thingSoC/TSOC_ESP32S/TSOC_ESP32S/eagleUp/eagleUp_TSOC_ESP32S_board_top.jpg

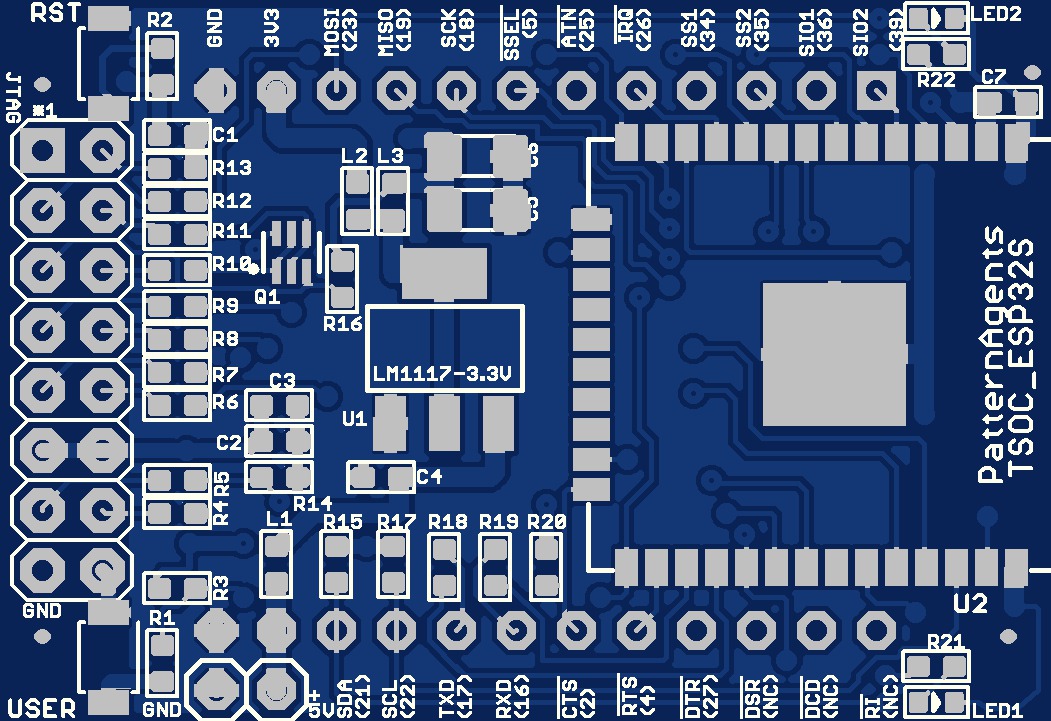
TSOC_ESP32S/eagleUp/eagleUp_TSOC_ESP32S_board_top.jpg
