thingSoC/TSOC_ESP32S/TSOC_ESP32S/images/product/Blynk_Screen_ESP32.jpg

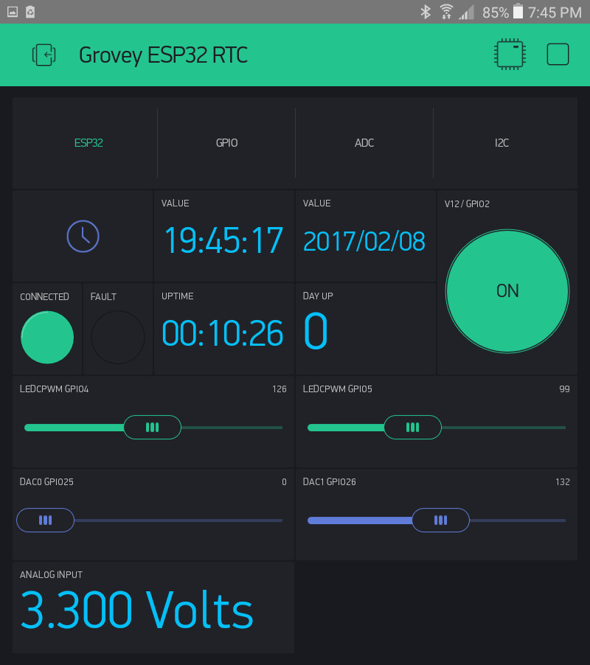
TSOC_ESP32S/images/product/Blynk_Screen_ESP32.jpg
