thingSoC/TSOC_ESP32S/TSOC_ESP32S/images/product/Screenshot_ESP32.jpg

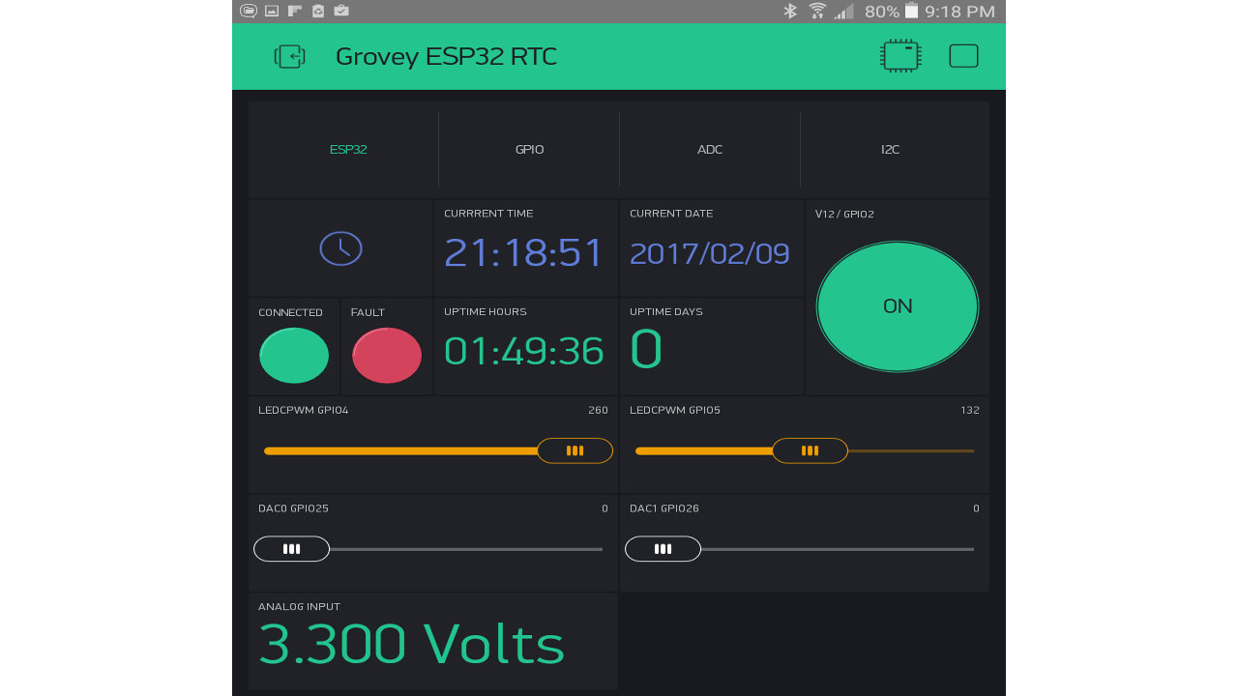
TSOC_ESP32S/images/product/Screenshot_ESP32.jpg
