thingSoC/TSOC_ESP32S/TSOC_ESP32S/images/product/Screenshot_GPIO.jpg

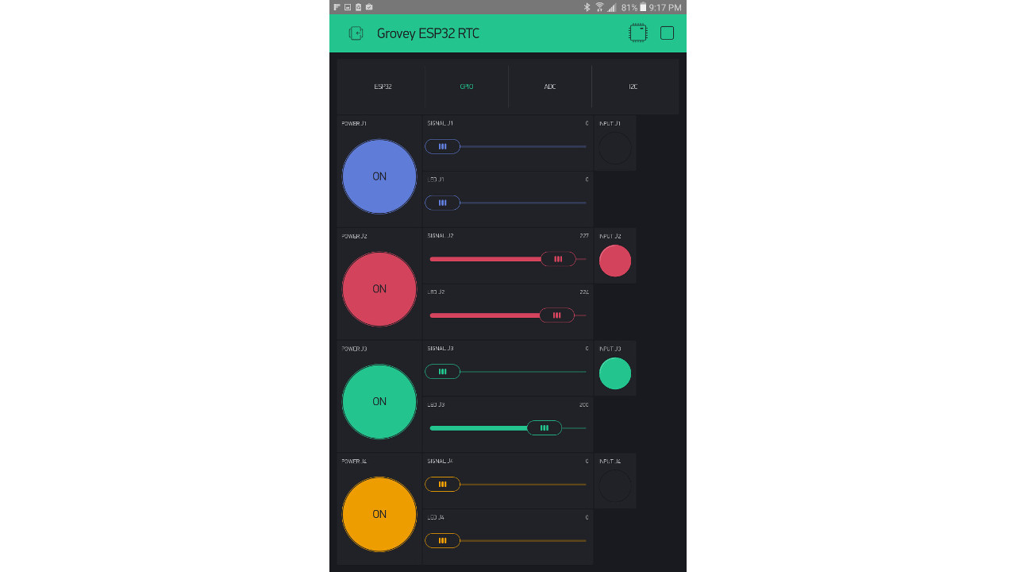
TSOC_ESP32S/images/product/Screenshot_GPIO.jpg
