thingSoC/TSOC_ESP32S/TSOC_ESP32S/images/product/TSOC_ESP32S.png

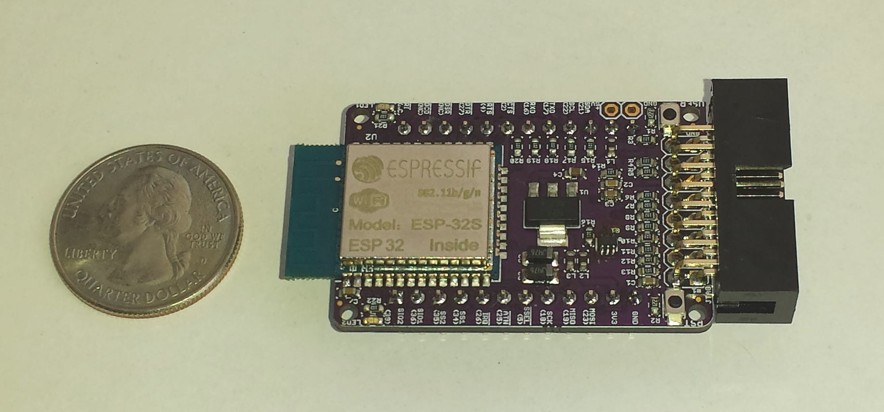
TSOC_ESP32S/images/product/TSOC_ESP32S.png
