thingSoC/TSOC_ESP32S/TSOC_ESP32S/images/product/TSOC_ESP32S_top.jpg

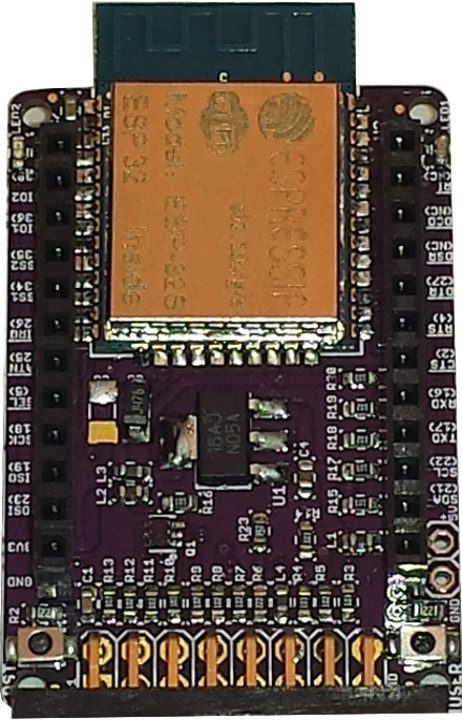
TSOC_ESP32S/images/product/TSOC_ESP32S_top.jpg
