thingSoC/TSOC_ESP32S/TSOC_ESP32S/images/product/TSOC_ESP32S_with FTDI_sqr.jpg

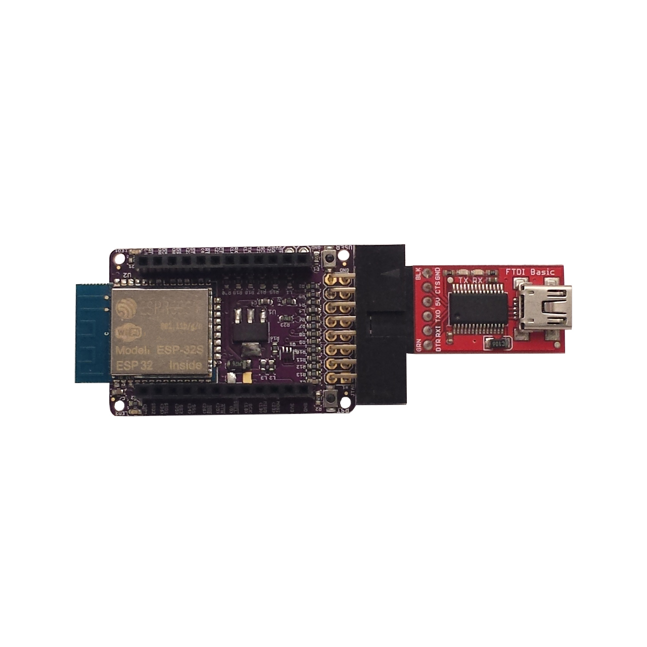
TSOC_ESP32S/images/product/TSOC_ESP32S_with FTDI_sqr.jpg
