thingSoC/TSOC_ESP32S/TSOC_ESP32S/images/product/TSOC_ESP32S_with_GSM_radio_long.jpg

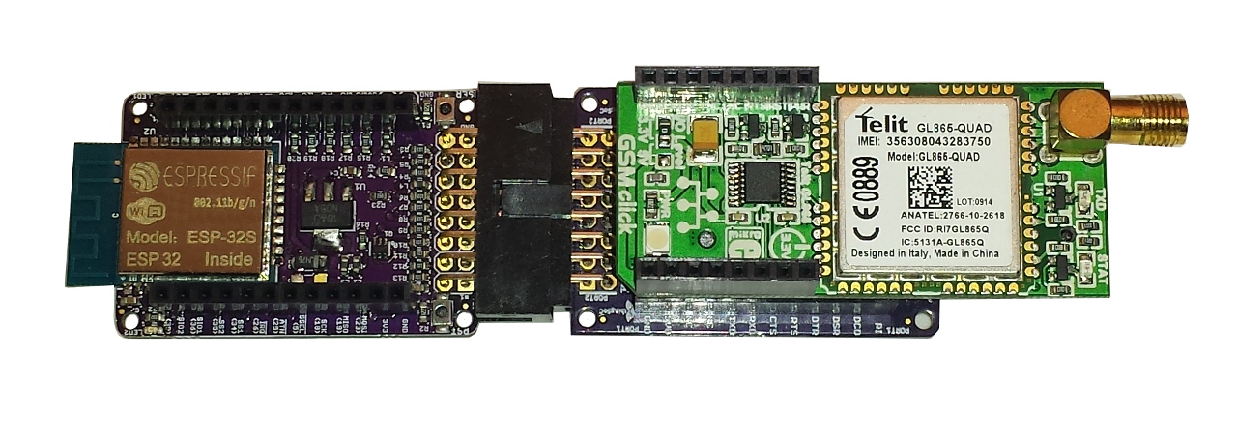
TSOC_ESP32S/images/product/TSOC_ESP32S_with_GSM_radio_long.jpg
