thingSoC/TSOC_ESP32S/TSOC_ESP32S/images/product/wifi_connect.jpg

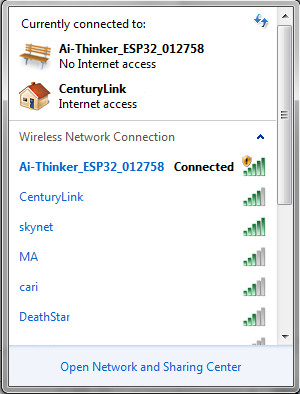
TSOC_ESP32S/images/product/wifi_connect.jpg
