thingSoC/TSOC_ESP32S/TSOC_ESP32S/images/product/with_PSoC4L.png

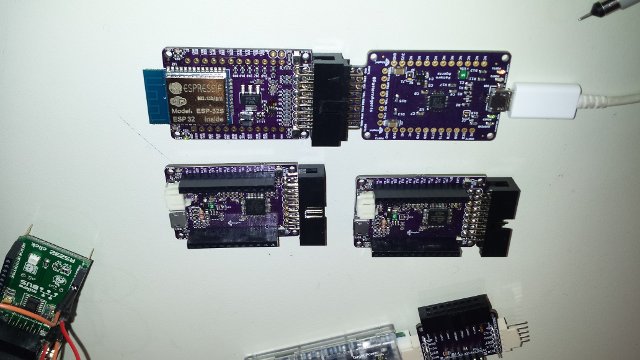
TSOC_ESP32S/images/product/with_PSoC4L.png
