thingSoC/TSOC_ESP32S/TSOC_ESP32S/images/TSOC_ESP32S_iso.png

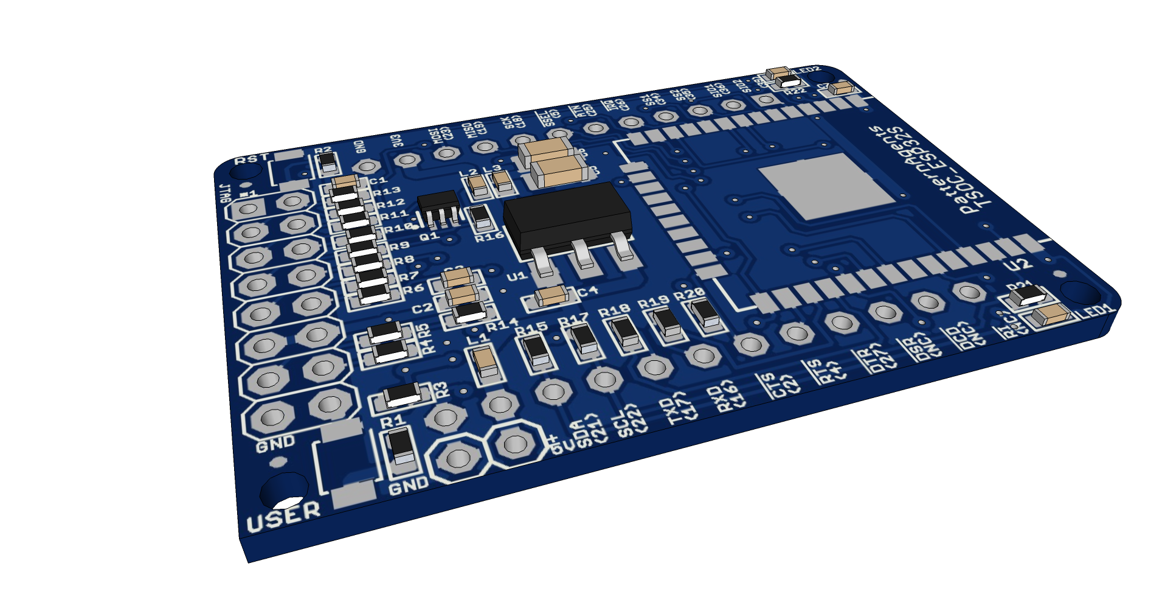
TSOC_ESP32S/images/TSOC_ESP32S_iso.png
